AdrianChemicz/FootController/PCB/LPC11U14_EvalBoard.sch

## KiCad design PCB/LPC11U14_EvalBoard.sch (2021-07-26)

Schematic: LPC11U14_EvalBoard.sch

Parts:
C1: 10nF
C2, C3, C4: 1uF
C5, C6, C7, C8, C12, C13: 100nF
C9, C10: 22pF
C11: 10k
CN1: USB-MINI-B
CN2, CN7: CONN_6X2
CN3: CONN_3
CN4, CN6: CONN_2X2
CN5, CN8: CONN_3X2
CN9, CN10: CONN_8
D1: LED
F1: GS2
FB1: 100MHz 600ohm 1,3A
R1: 2200
R2: 1500
R3, R4: 33
R5, R6, R8, R9, R10, R11, R12, R13, R14, R15, R16, R17, R18, R19, R20, R21, R22, R23, R24: 10k
R7: 100
R25: 0
U1: TCR2EF33
U2: LPC11U24FHI33/301
X1: 12MHz

Notes on the sheet:
POWER SUPLY
CONNECTORS
MICROCONTROLLER
